NovaCentrix/chris-tracer-pcb/tracer.packages3d/plcc-2-package-3d.stp

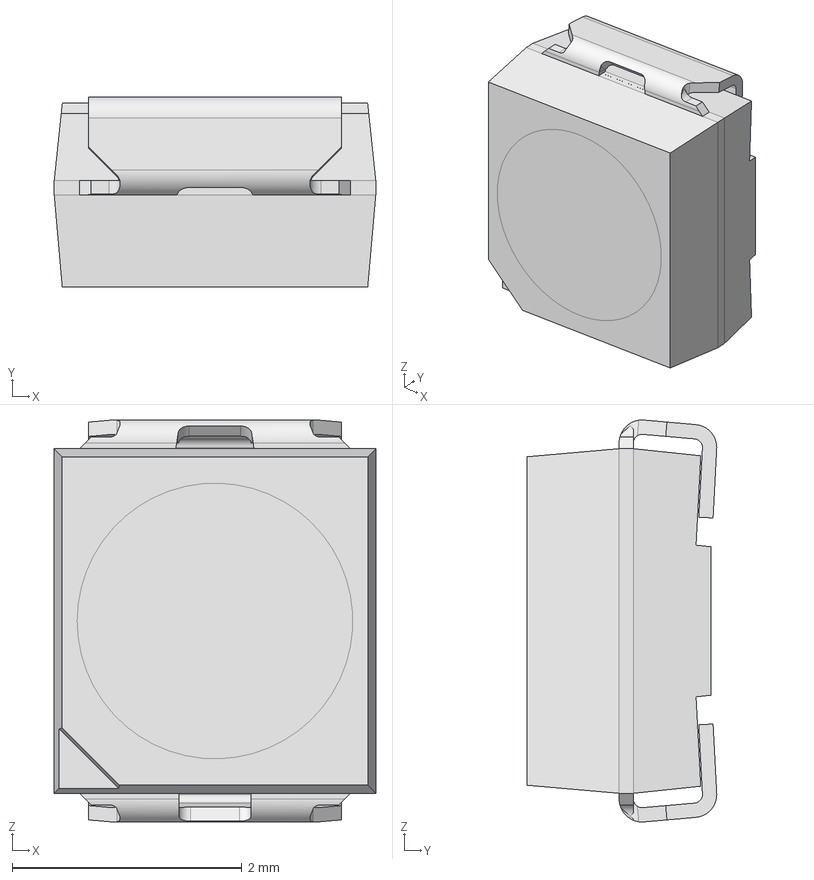
[picture p20: CAD file, 2021-05-20]
tracer.packages3d/plcc-2-package-3d.stp
2.80 x 1.65 x 3.50 mm
