NovaCentrix/chris-tracer-pcb/tracer.packages3d/9913_stp.stp

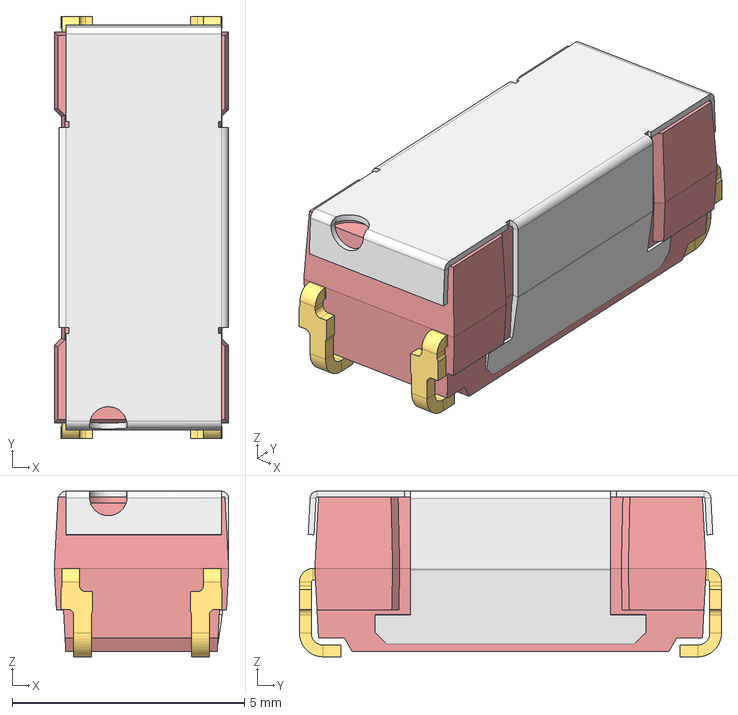
[picture p21: CAD file, 2021-05-20]
tracer.packages3d/9913_stp.stp
3.76 x 9.09 x 3.57 mm
