NovaCentrix/chris-tracer-pcb/tracer.packages3d/LED_1210_3225Metric.step

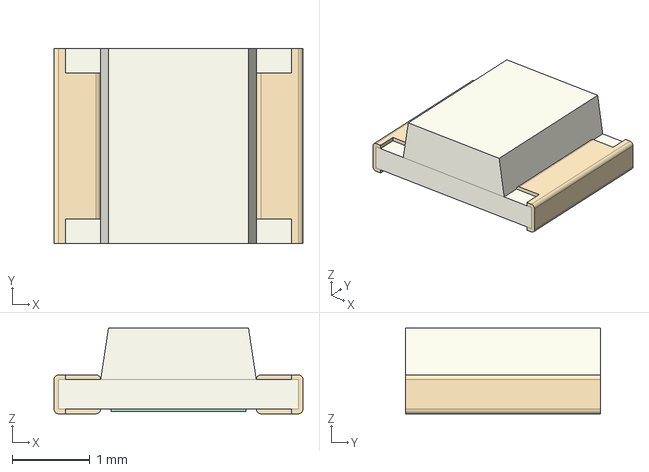
[picture p22: CAD file, 2021-05-20]
tracer.packages3d/LED_1210_3225Metric.step
3.20 x 2.50 x 1.10 mm
