NovaCentrix/chris-tracer-pcb/tracer.packages3d/Molex_KK-254_AE-6410-04A_1x04_P2.54mm_Vertical.step

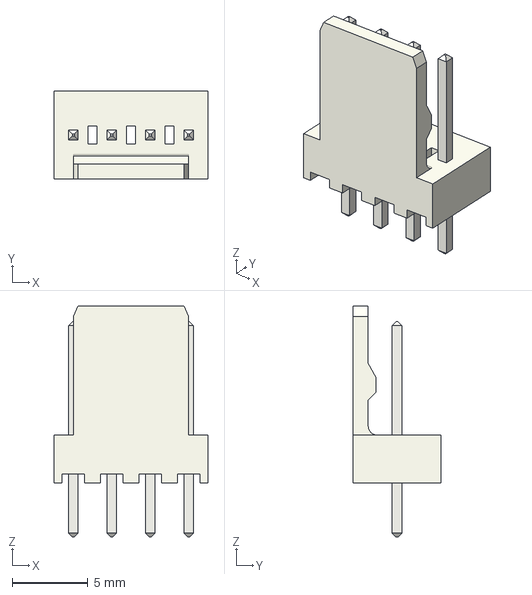
[picture p23: CAD file, 2021-05-20]
tracer.packages3d/Molex_KK-254_AE-6410-04A_1x04_P2.54mm_Vertical.step
10.2 x 5.80 x 15.3 mm
