NovaCentrix/chris-tracer-pcb/tracer.packages3d/DFN1006-2.stp

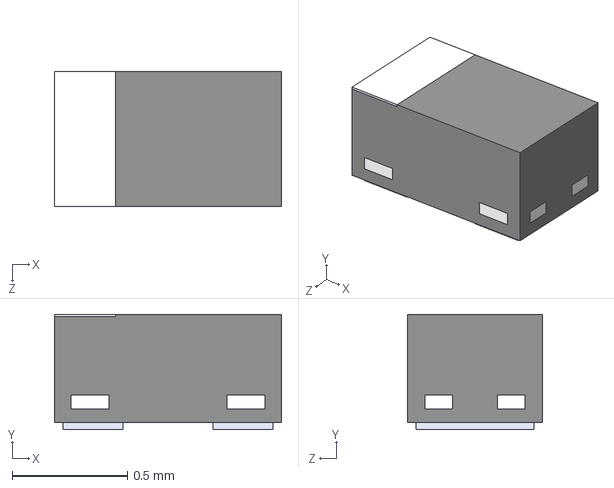
[picture p24: CAD file, 2021-05-20]
tracer.packages3d/DFN1006-2.stp
0.985 x 0.5 x 0.585 mm
